UniversalScientificTechnologies/TelescopeFocuser/DOC/SRC/img/DSC_8367x.JPG

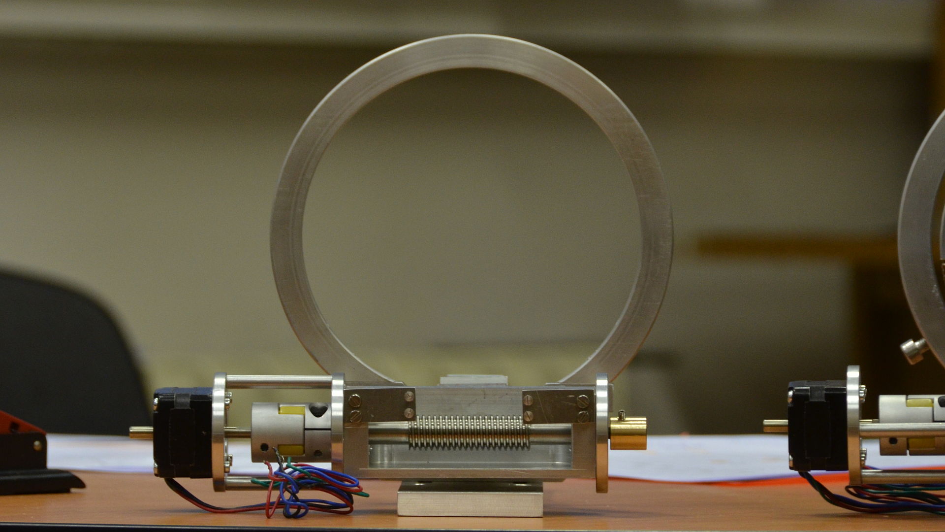
DOC/SRC/img/DSC_8367x.JPG
