UniversalScientificTechnologies/TelescopeFocuser/DOC/SRC/img/P1020715.JPG

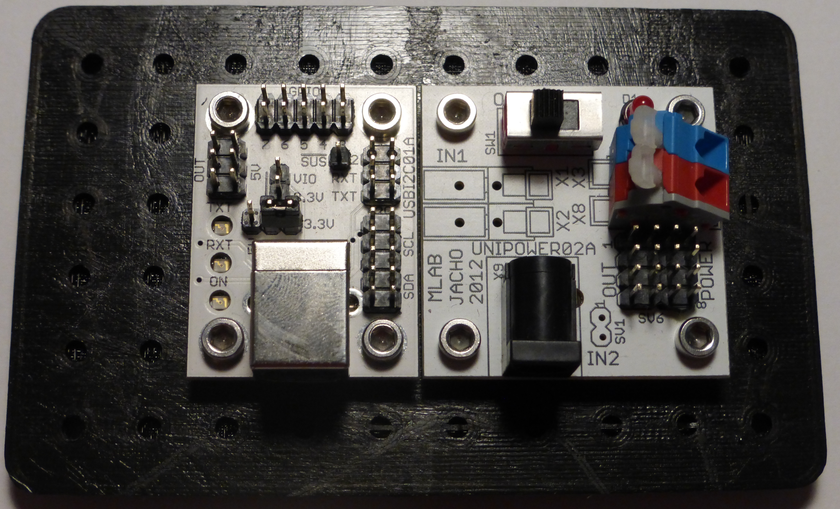
DOC/SRC/img/P1020715.JPG
