UniversalScientificTechnologies/TelescopeFocuser/DOC/SRC/img/P1020728.JPG

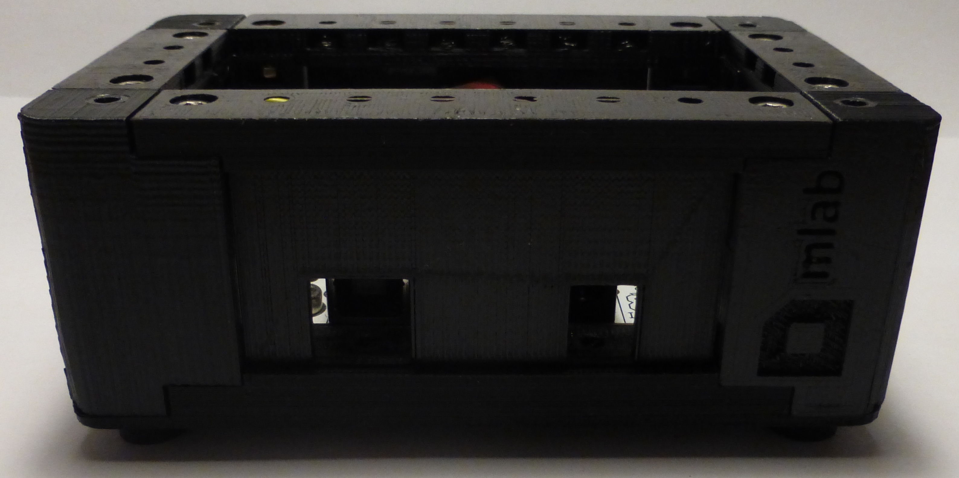
DOC/SRC/img/P1020728.JPG
