UniversalScientificTechnologies/TelescopeFocuser/DOC/SRC/img/P1020730.JPG

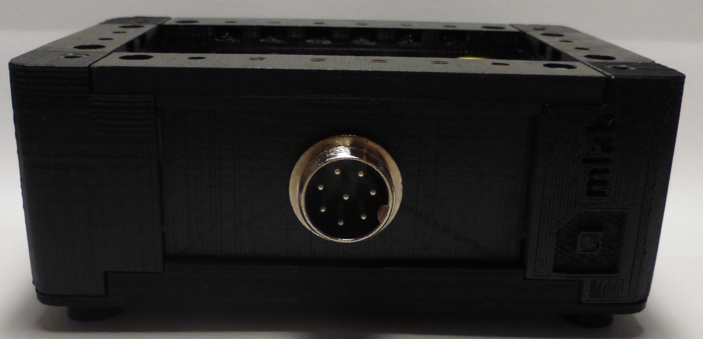
DOC/SRC/img/P1020730.JPG
