UniversalScientificTechnologies/TelescopeFocuser/DOC/SRC/img/P1020737.JPG

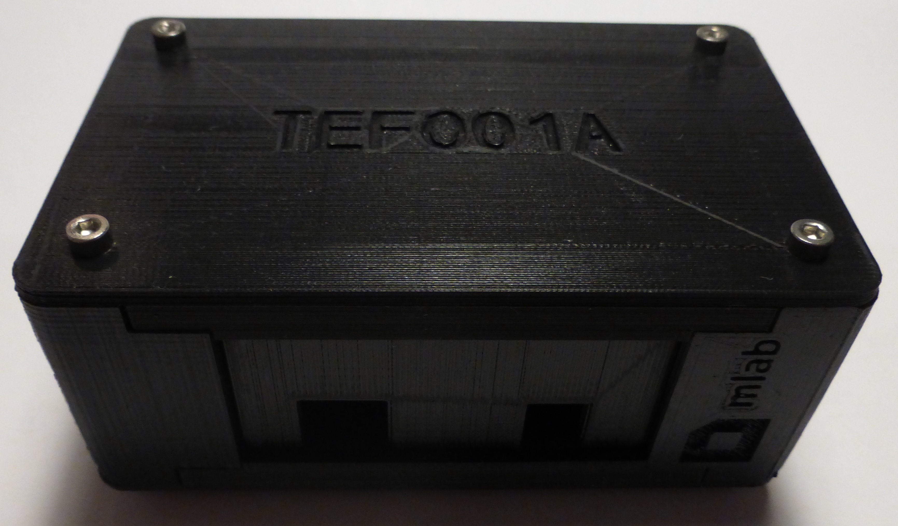
DOC/SRC/img/P1020737.JPG
