UniversalScientificTechnologies/TelescopeFocuser/DOC/SRC/img/P1020746.JPG

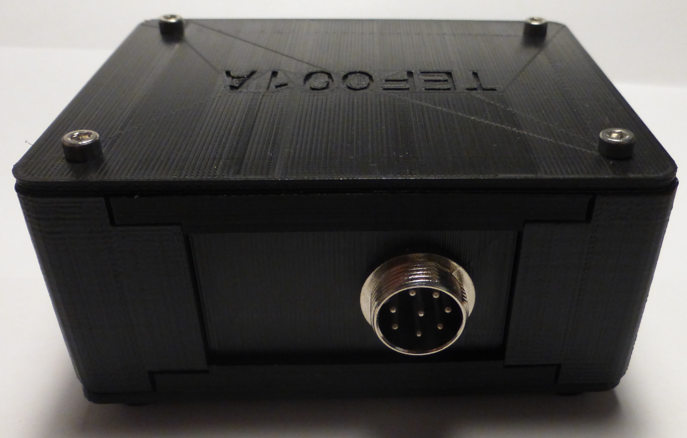
DOC/SRC/img/P1020746.JPG
